yizhizhu222/Robot/Software/Upper_Computer/OrangePi-ZERO3.pdf

D | D

# 1.Note that the voltage of SOC GPIO must matches the

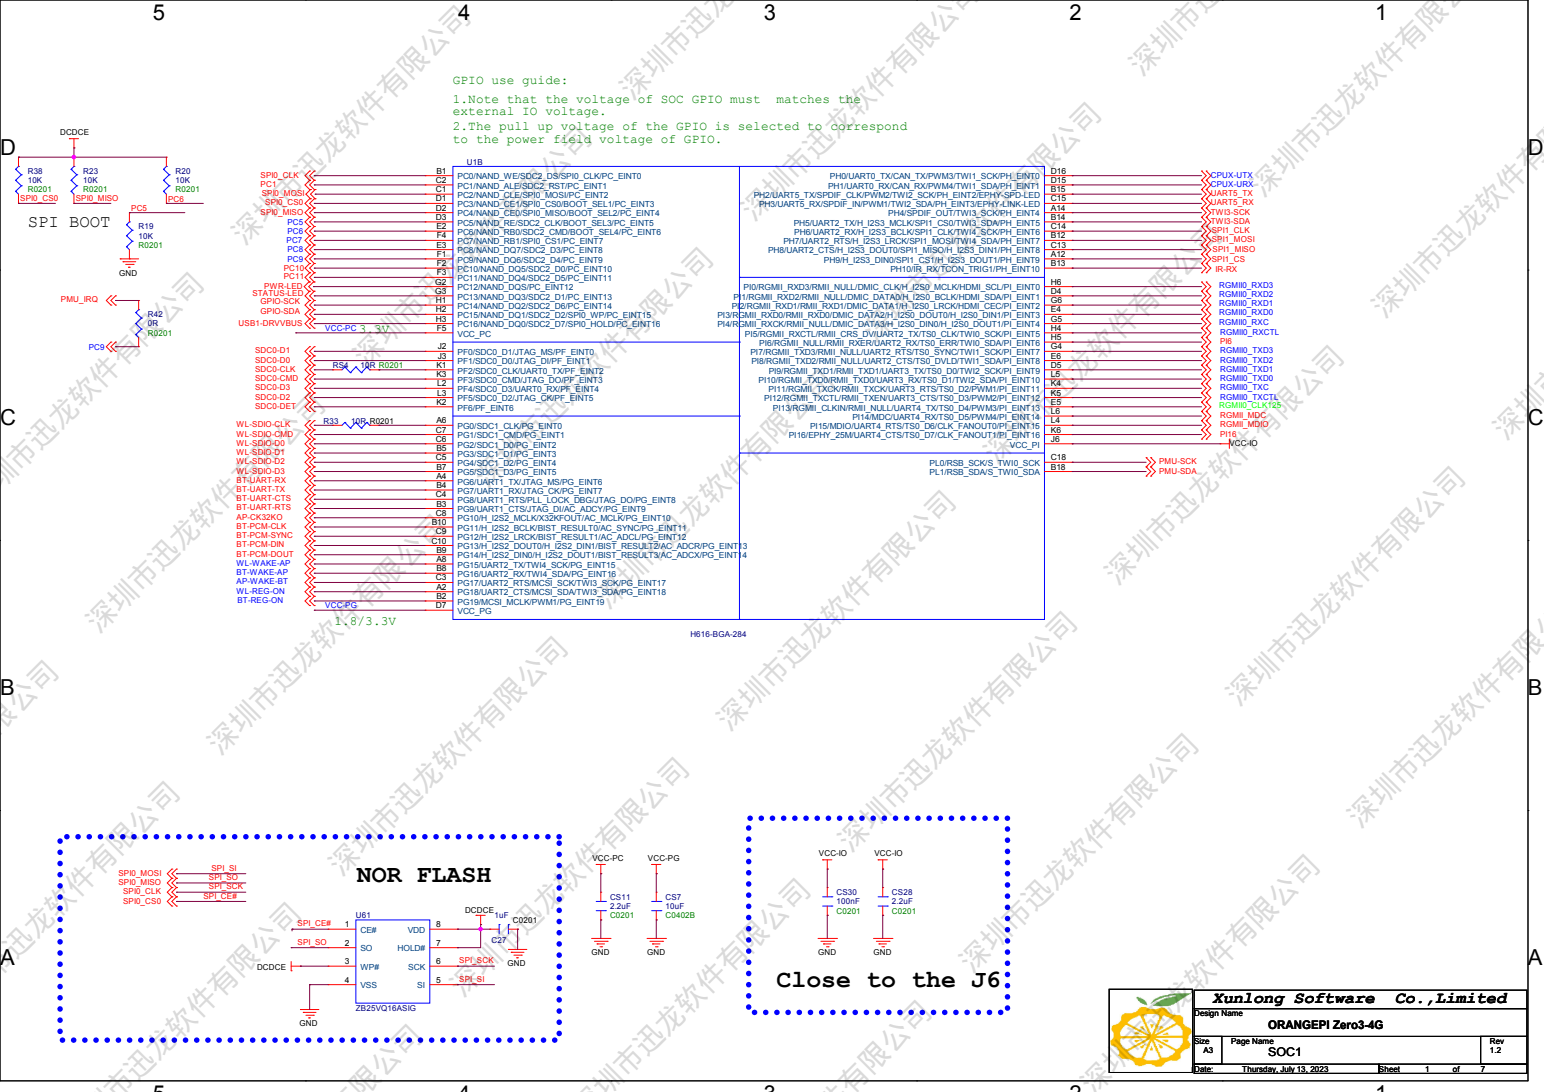
[picture p6: page 1]

深圳市迅龙软件有限公司 深圳市迅龙软件有限公司 深圳市迅龙软件有限公司 深圳市迅龙软件有限公司 深圳市迅龙软件有限公司 深圳市迅龙软件有限公司 深圳市迅龙软件有限公司 深圳市迅龙软件有限公司 深圳市迅龙软件有限公司 深圳市迅龙软件有限公司 深圳市迅龙软件有限公司 深圳市迅龙软件有限公司 深圳市迅龙软件有限公司 深圳市迅龙软件有限公司 深圳市迅龙软件有限公司 深圳市迅龙软件有限公司 深圳市迅龙软件有限公司 深圳市迅龙软件有限公司 深圳市迅龙软件有限公司 深圳市迅龙软件有限公司 深圳市迅龙软件有限公司 深圳市迅龙软件有限公司 深圳市迅龙软件有限公司 深圳市迅龙软件有限公司 深圳市迅龙软件有限公司 深圳市迅龙软件有限公司 深圳市迅龙软件有限公司 深圳市迅龙软件有限公司 深圳市迅龙软件有限公司 深圳市迅龙软件有限公司 深圳市迅龙软件有限公司 深圳市迅龙软件有限公司 深圳市迅龙软件有限公司 深圳市迅龙软件有限公司 深圳市迅龙软件有限公司 深圳市迅龙软件有限公司 深圳市迅龙软件有限公司 深圳市迅龙软件有限公司 深圳市迅龙软件有限公司 深圳市迅龙软件有限公司

GPIO use guide:
external IO voltage.
2.The pull up voltage of the GPIO is selected to correspond
to the power field voltage of GPIO.

Xunlong Software Co.,Limited

D | D

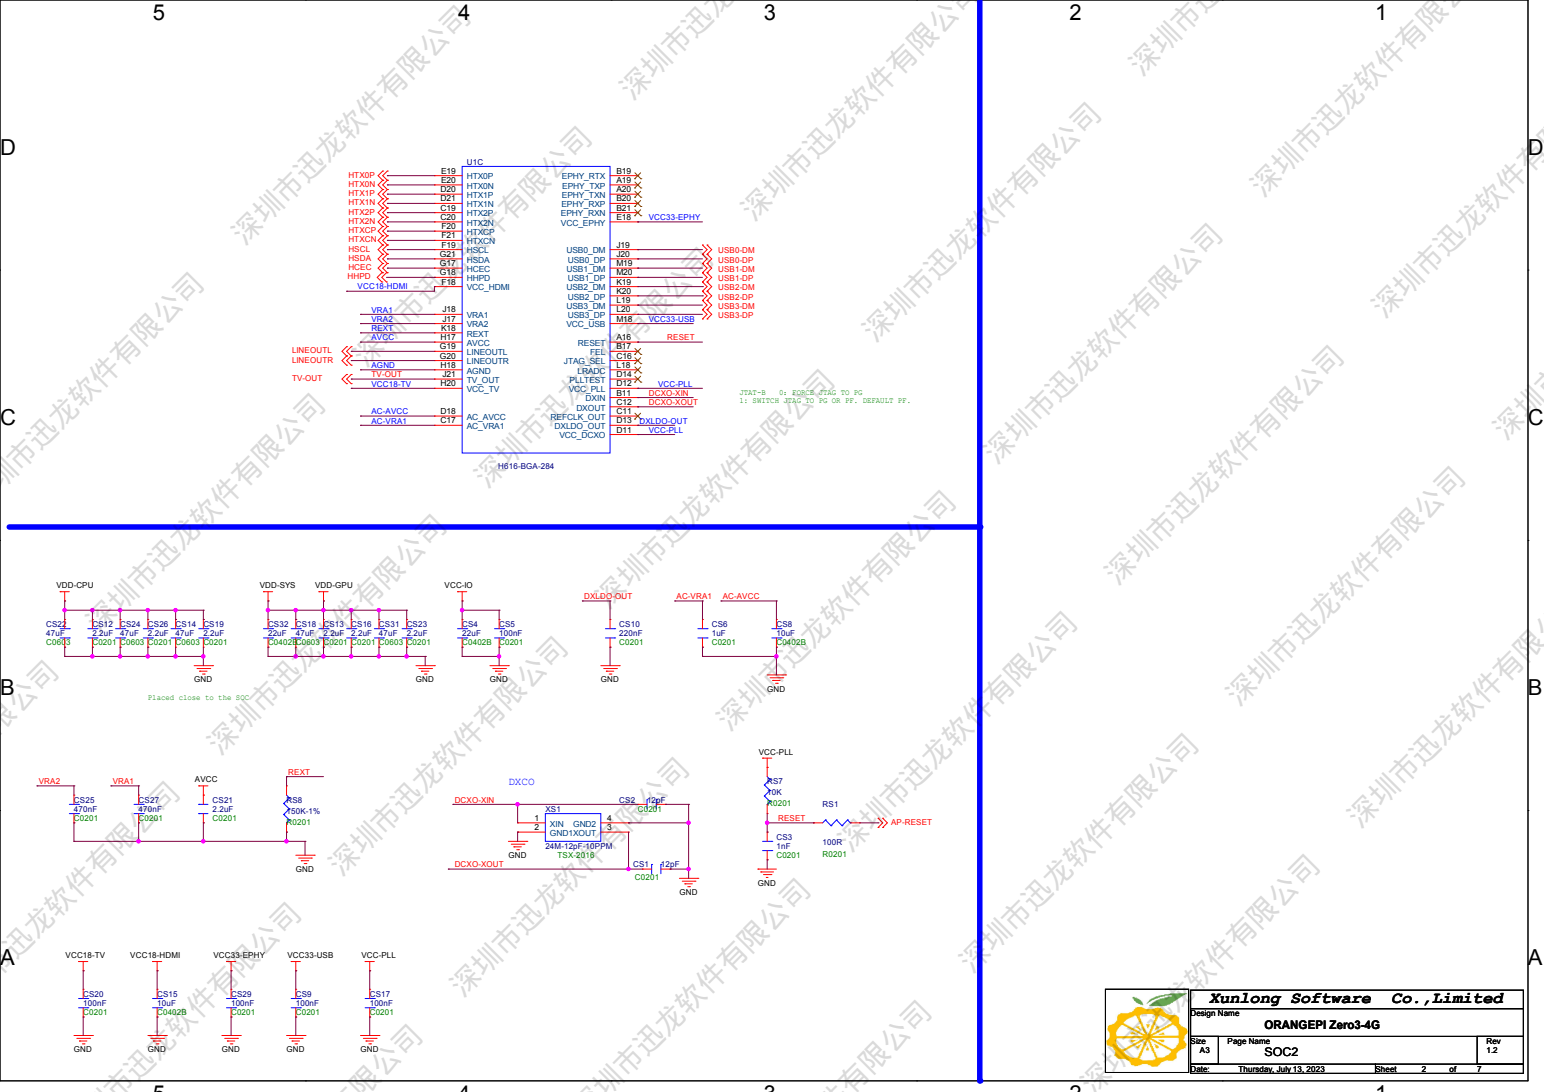
[picture p7: page 2]

深圳市迅龙软件有限公司 深圳市迅龙软件有限公司 深圳市迅龙软件有限公司 深圳市迅龙软件有限公司 深圳市迅龙软件有限公司 深圳市迅龙软件有限公司 深圳市迅龙软件有限公司 深圳市迅龙软件有限公司 深圳市迅龙软件有限公司 深圳市迅龙软件有限公司 深圳市迅龙软件有限公司 深圳市迅龙软件有限公司 深圳市迅龙软件有限公司 深圳市迅龙软件有限公司 深圳市迅龙软件有限公司 深圳市迅龙软件有限公司 深圳市迅龙软件有限公司 深圳市迅龙软件有限公司 深圳市迅龙软件有限公司 深圳市迅龙软件有限公司 深圳市迅龙软件有限公司 深圳市迅龙软件有限公司 深圳市迅龙软件有限公司 深圳市迅龙软件有限公司 深圳市迅龙软件有限公司 深圳市迅龙软件有限公司 深圳市迅龙软件有限公司 深圳市迅龙软件有限公司 深圳市迅龙软件有限公司 深圳市迅龙软件有限公司 深圳市迅龙软件有限公司 深圳市迅龙软件有限公司 深圳市迅龙软件有限公司 深圳市迅龙软件有限公司 深圳市迅龙软件有限公司 深圳市迅龙软件有限公司 深圳市迅龙软件有限公司 深圳市迅龙软件有限公司 深圳市迅龙软件有限公司 深圳市迅龙软件有限公司

JTAT-B 0：FORCE JTAG TO PG
1: SWITCH JTAG TO PG OR PF. DEFAULT PF.

Placed close to the SOC

Xunlong Software Co.,Limited

D | D

# LPDDR4

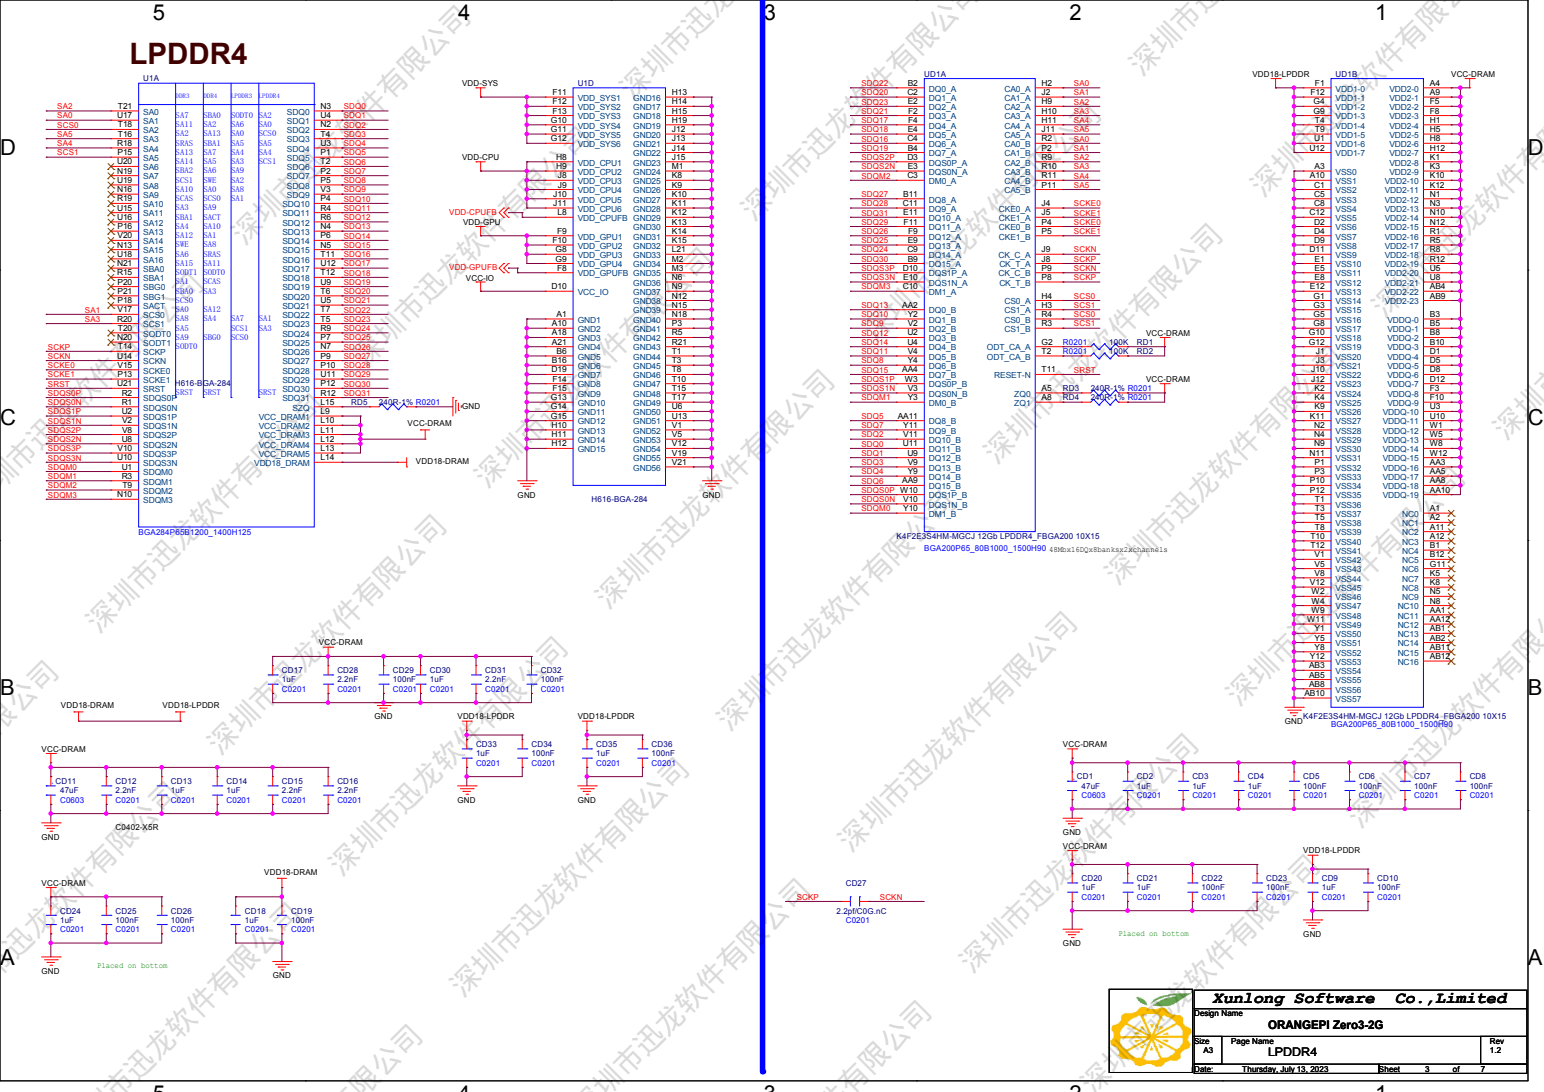
[picture p8: page 3]

深圳市迅龙软件有限公司 深圳市迅龙软件有限公司 深圳市迅龙软件有限公司 深圳市迅龙软件有限公司 深圳市迅龙软件有限公司 深圳市迅龙软件有限公司 深圳市迅龙软件有限公司 深圳市迅龙软件有限公司 深圳市迅龙软件有限公司 深圳市迅龙软件有限公司 深圳市迅龙软件有限公司 深圳市迅龙软件有限公司 深圳市迅龙软件有限公司 深圳市迅龙软件有限公司 深圳市迅龙软件有限公司 深圳市迅龙软件有限公司 深圳市迅龙软件有限公司 深圳市迅龙软件有限公司 深圳市迅龙软件有限公司 深圳市迅龙软件有限公司 深圳市迅龙软件有限公司 深圳市迅龙软件有限公司 深圳市迅龙软件有限公司 深圳市迅龙软件有限公司 深圳市迅龙软件有限公司 深圳市迅龙软件有限公司 深圳市迅龙软件有限公司 深圳市迅龙软件有限公司 深圳市迅龙软件有限公司 深圳市迅龙软件有限公司 深圳市迅龙软件有限公司 深圳市迅龙软件有限公司 深圳市迅龙软件有限公司 深圳市迅龙软件有限公司 深圳市迅龙软件有限公司 深圳市迅龙软件有限公司 深圳市迅龙软件有限公司 深圳市迅龙软件有限公司 深圳市迅龙软件有限公司 深圳市迅龙软件有限公司

Xunlong Software Co.,Limited

# TPYE-C

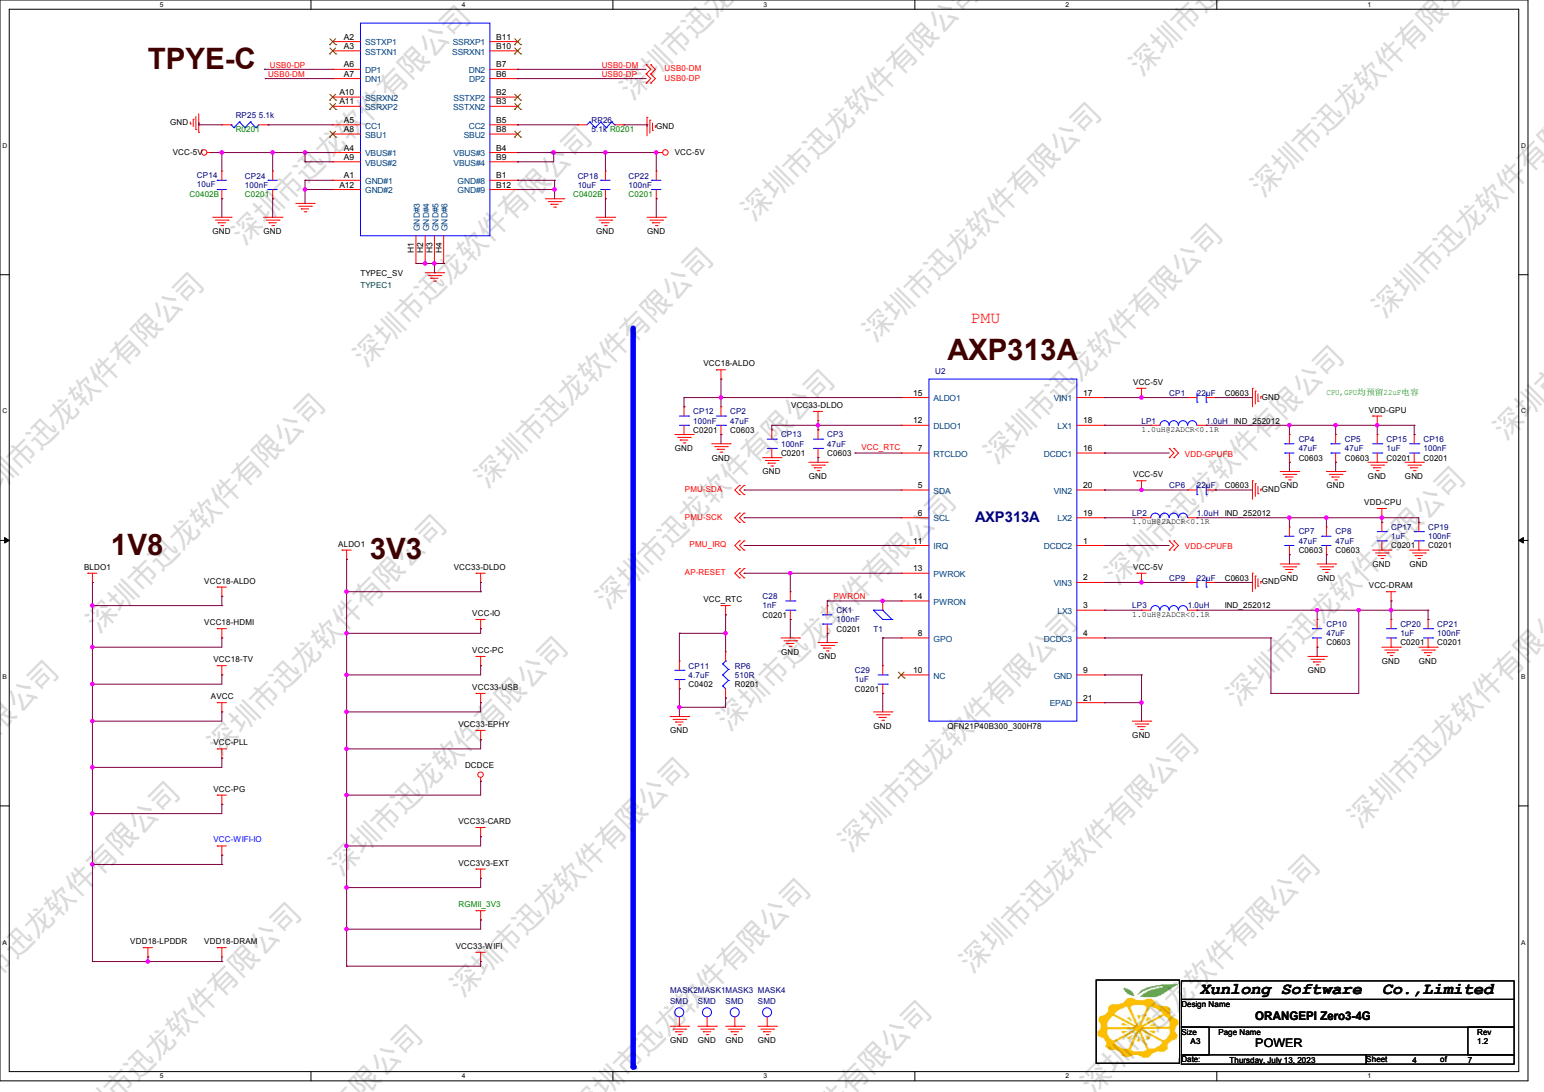
[picture p9: page 4]

深圳市迅龙软件有限公司 深圳市迅龙软件有限公司 深圳市迅龙软件有限公司 深圳市迅龙软件有限公司 深圳市迅龙软件有限公司 深圳市迅龙软件有限公司 深圳市迅龙软件有限公司 深圳市迅龙软件有限公司 深圳市迅龙软件有限公司 深圳市迅龙软件有限公司 深圳市迅龙软件有限公司 深圳市迅龙软件有限公司 深圳市迅龙软件有限公司 深圳市迅龙软件有限公司 深圳市迅龙软件有限公司 深圳市迅龙软件有限公司 深圳市迅龙软件有限公司 深圳市迅龙软件有限公司 深圳市迅龙软件有限公司 深圳市迅龙软件有限公司 深圳市迅龙软件有限公司 深圳市迅龙软件有限公司 深圳市迅龙软件有限公司 深圳市迅龙软件有限公司 深圳市迅龙软件有限公司 深圳市迅龙软件有限公司 深圳市迅龙软件有限公司 深圳市迅龙软件有限公司 深圳市迅龙软件有限公司 深圳市迅龙软件有限公司 深圳市迅龙软件有限公司 深圳市迅龙软件有限公司 深圳市迅龙软件有限公司 深圳市迅龙软件有限公司 深圳市迅龙软件有限公司 深圳市迅龙软件有限公司 深圳市迅龙软件有限公司 深圳市迅龙软件有限公司 深圳市迅龙软件有限公司 深圳市迅龙软件有限公司

Xunlong Software Co.,Limited

D | D

# T CARD

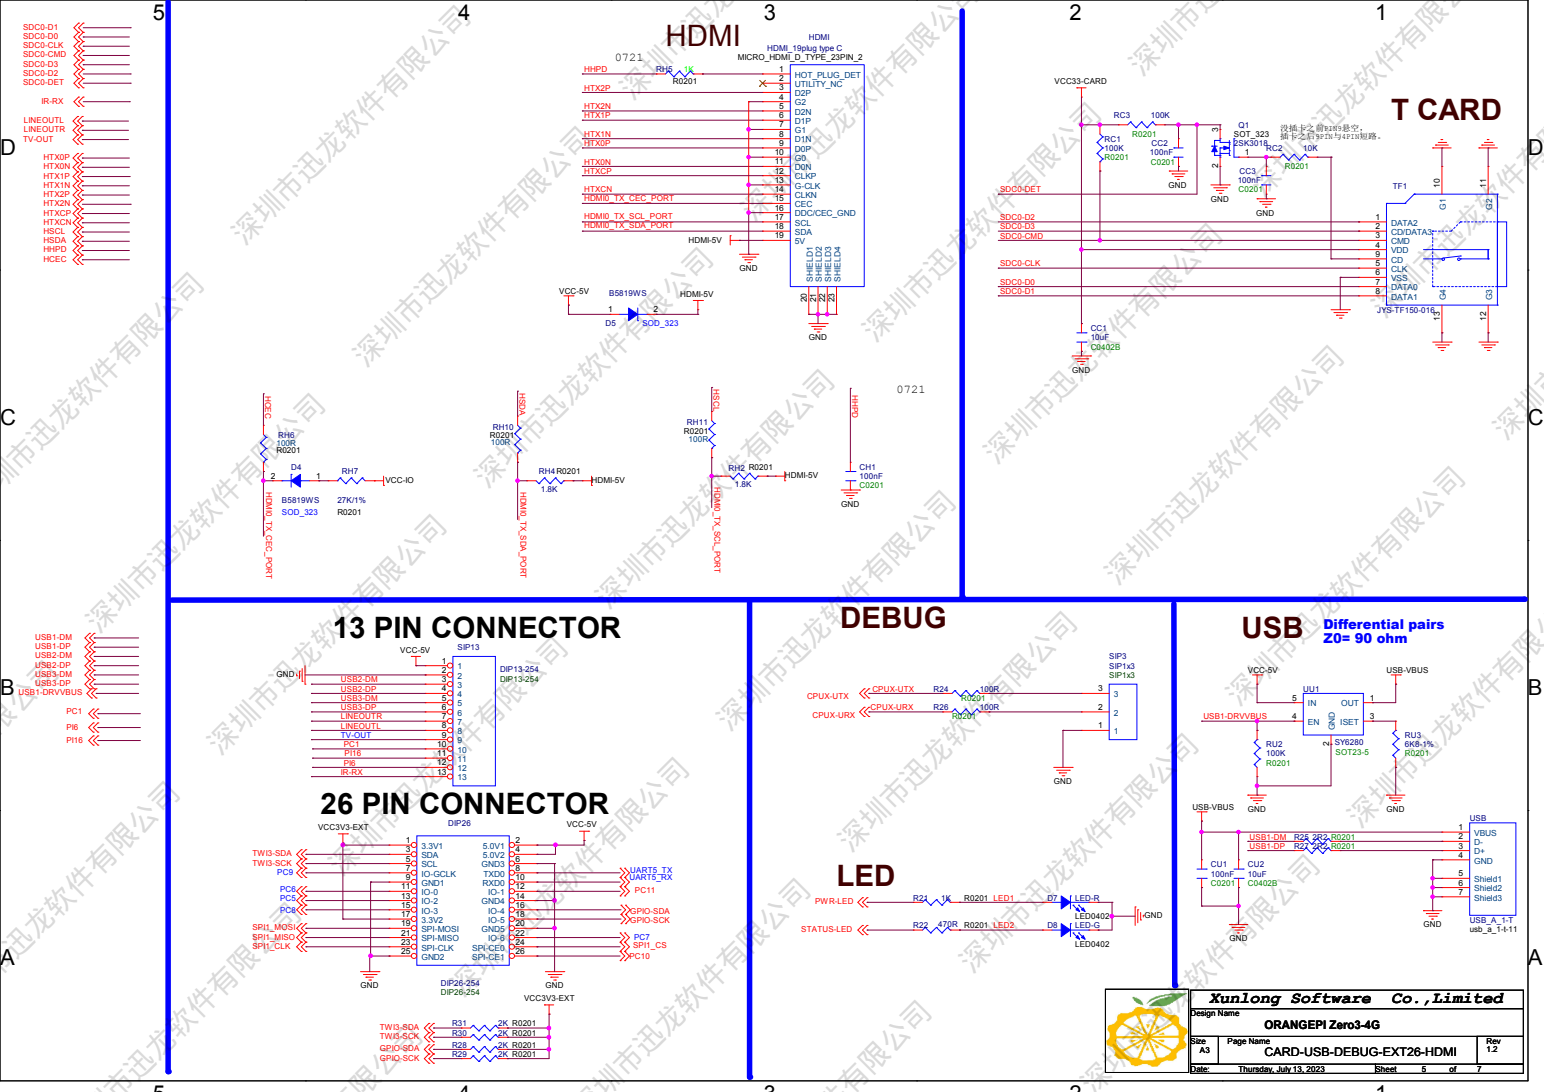
[picture p10: page 5]

深圳市迅龙软件有限公司 深圳市迅龙软件有限公司 深圳市迅龙软件有限公司 深圳市迅龙软件有限公司 深圳市迅龙软件有限公司 深圳市迅龙软件有限公司 深圳市迅龙软件有限公司 深圳市迅龙软件有限公司 深圳市迅龙软件有限公司 深圳市迅龙软件有限公司 深圳市迅龙软件有限公司 深圳市迅龙软件有限公司 深圳市迅龙软件有限公司 深圳市迅龙软件有限公司 深圳市迅龙软件有限公司 深圳市迅龙软件有限公司 深圳市迅龙软件有限公司 深圳市迅龙软件有限公司 深圳市迅龙软件有限公司 深圳市迅龙软件有限公司 深圳市迅龙软件有限公司 深圳市迅龙软件有限公司 深圳市迅龙软件有限公司 深圳市迅龙软件有限公司 深圳市迅龙软件有限公司 深圳市迅龙软件有限公司 深圳市迅龙软件有限公司 深圳市迅龙软件有限公司 深圳市迅龙软件有限公司 深圳市迅龙软件有限公司 深圳市迅龙软件有限公司 深圳市迅龙软件有限公司 深圳市迅龙软件有限公司 深圳市迅龙软件有限公司 深圳市迅龙软件有限公司 深圳市迅龙软件有限公司 深圳市迅龙软件有限公司 深圳市迅龙软件有限公司 深圳市迅龙软件有限公司 深圳市迅龙软件有限公司

Xunlong Software Co.,Limited

CARD-USB-DEBUG-EXT26-HDMI

# Differential pairs Z0= 100 ohm

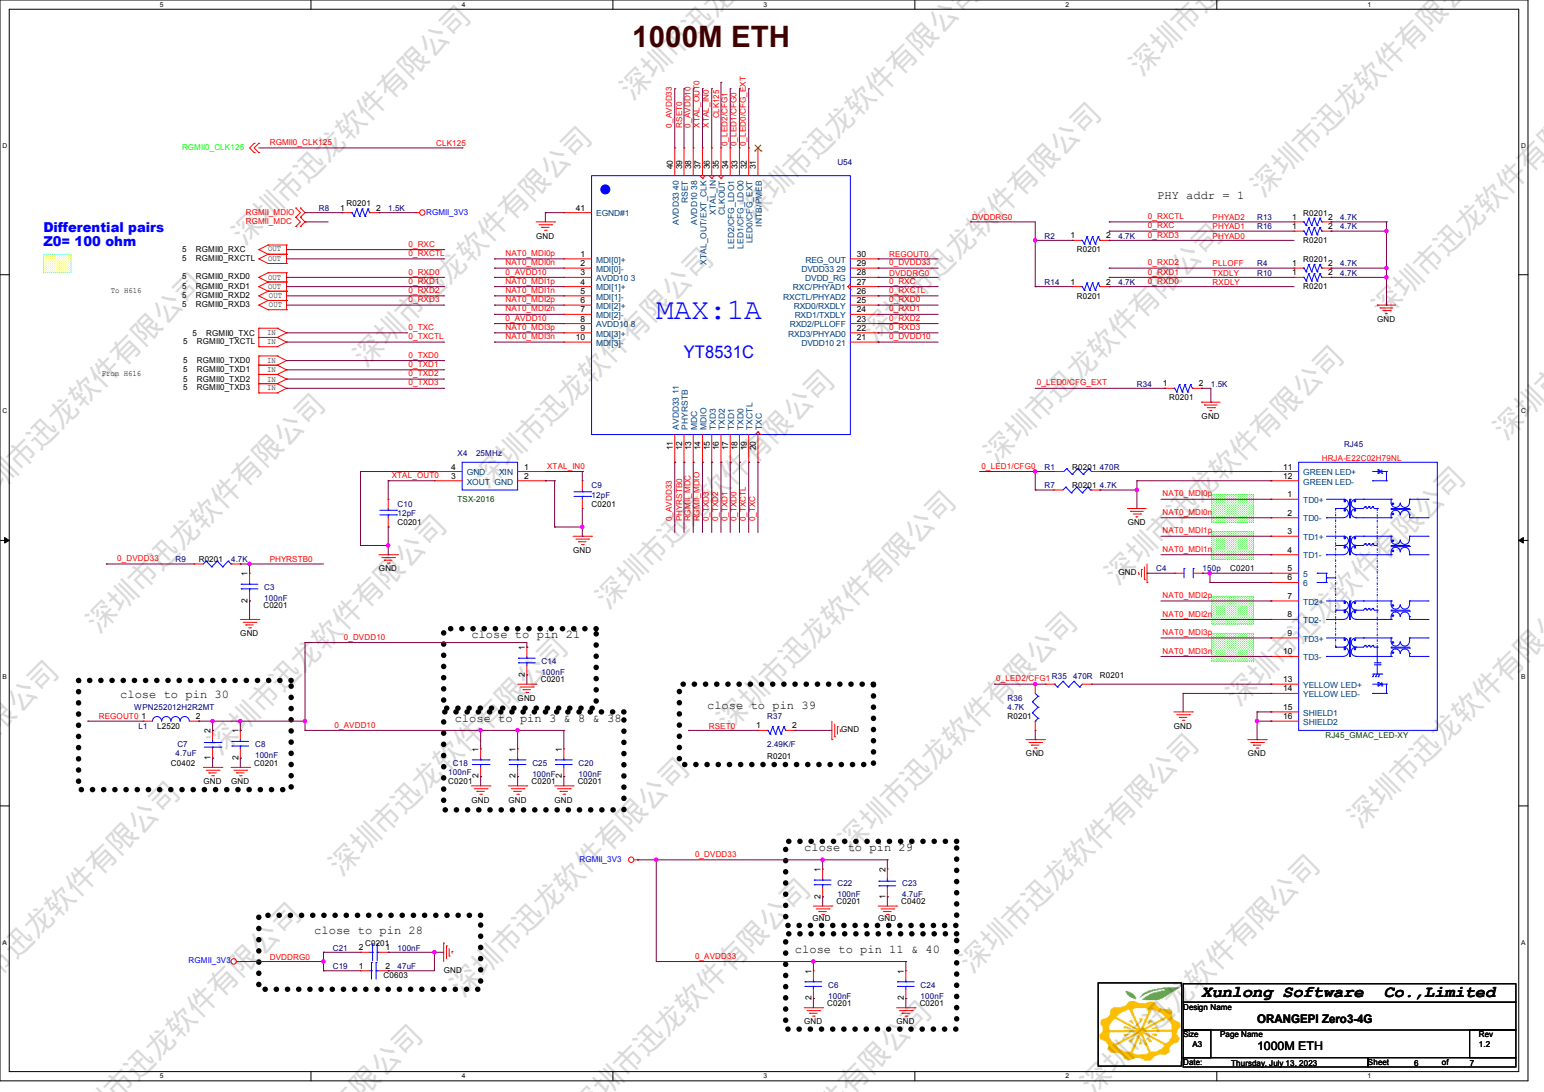
[picture p11: page 6]

深圳市迅龙软件有限公司 深圳市迅龙软件有限公司 深圳市迅龙软件有限公司 深圳市迅龙软件有限公司 深圳市迅龙软件有限公司 深圳市迅龙软件有限公司 深圳市迅龙软件有限公司 深圳市迅龙软件有限公司 深圳市迅龙软件有限公司 深圳市迅龙软件有限公司 深圳市迅龙软件有限公司 深圳市迅龙软件有限公司 深圳市迅龙软件有限公司 深圳市迅龙软件有限公司 深圳市迅龙软件有限公司 深圳市迅龙软件有限公司 深圳市迅龙软件有限公司 深圳市迅龙软件有限公司 深圳市迅龙软件有限公司 深圳市迅龙软件有限公司 深圳市迅龙软件有限公司 深圳市迅龙软件有限公司 深圳市迅龙软件有限公司 深圳市迅龙软件有限公司 深圳市迅龙软件有限公司 深圳市迅龙软件有限公司 深圳市迅龙软件有限公司 深圳市迅龙软件有限公司 深圳市迅龙软件有限公司 深圳市迅龙软件有限公司 深圳市迅龙软件有限公司 深圳市迅龙软件有限公司 深圳市迅龙软件有限公司 深圳市迅龙软件有限公司 深圳市迅龙软件有限公司 深圳市迅龙软件有限公司 深圳市迅龙软件有限公司 深圳市迅龙软件有限公司 深圳市迅龙软件有限公司 深圳市迅龙软件有限公司

Xunlong Software Co.,Limited

D | D

### 50Ω,TOP参考LAYER3

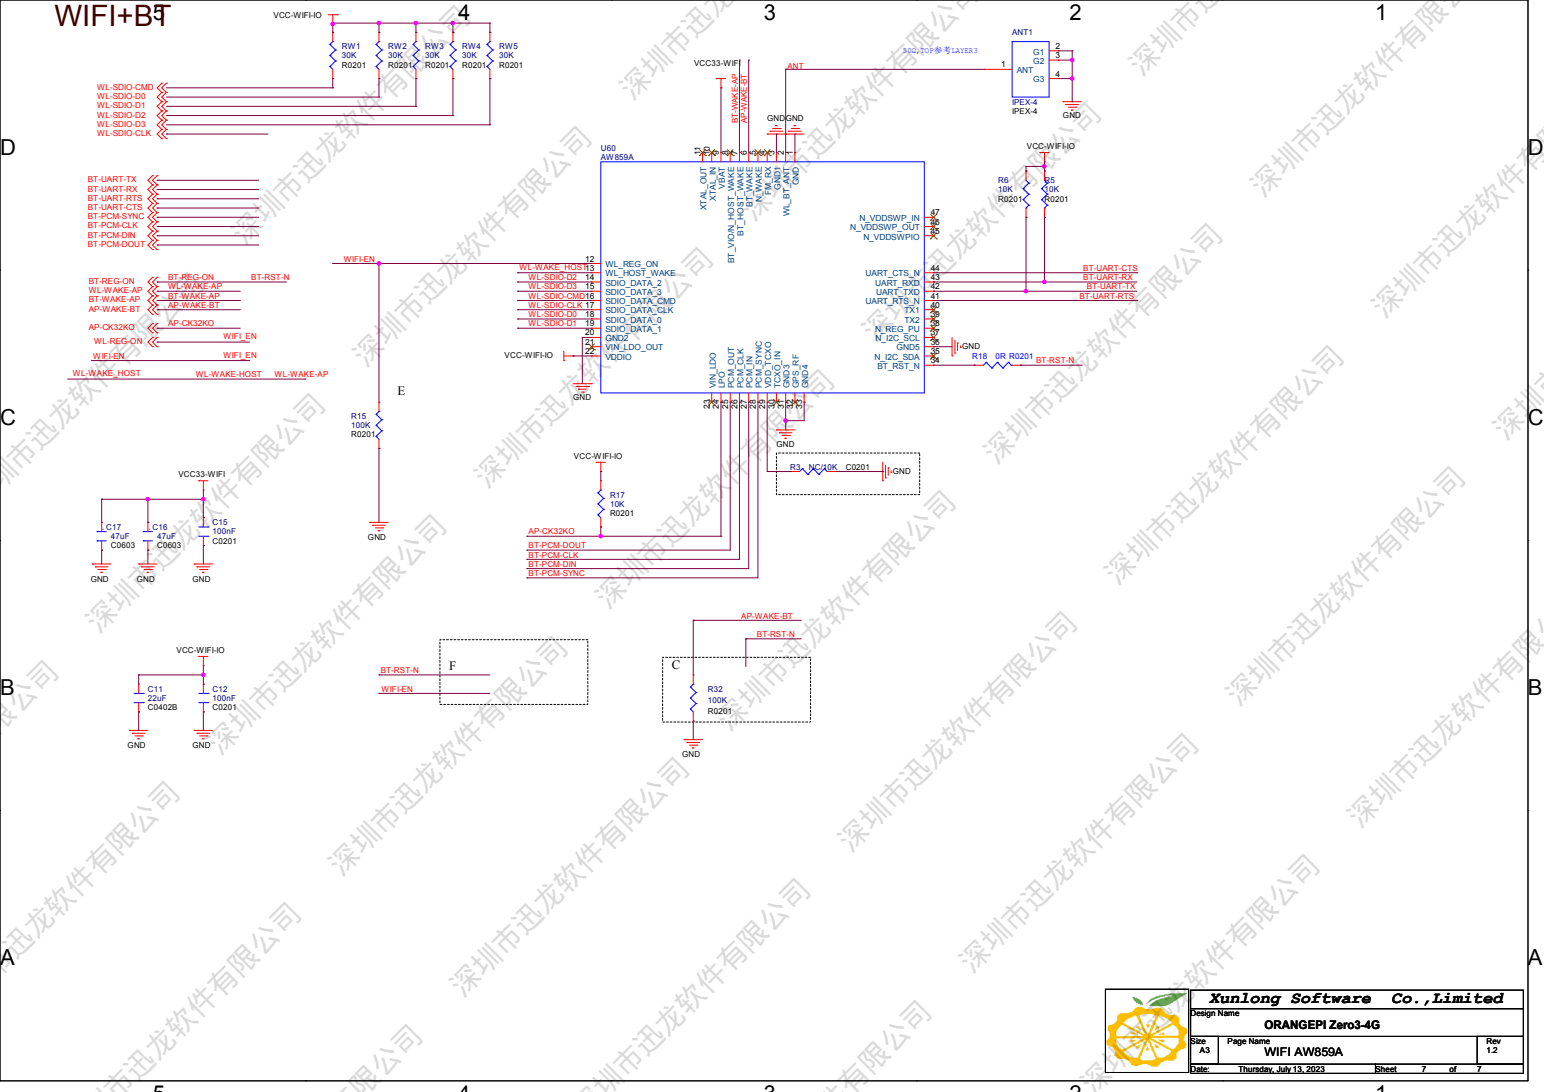
[picture p12: page 7]

深圳市迅龙软件有限公司 深圳市迅龙软件有限公司 深圳市迅龙软件有限公司 深圳市迅龙软件有限公司 深圳市迅龙软件有限公司 深圳市迅龙软件有限公司 深圳市迅龙软件有限公司 深圳市迅龙软件有限公司 深圳市迅龙软件有限公司 深圳市迅龙软件有限公司 深圳市迅龙软件有限公司 深圳市迅龙软件有限公司 深圳市迅龙软件有限公司 深圳市迅龙软件有限公司 深圳市迅龙软件有限公司 深圳市迅龙软件有限公司 深圳市迅龙软件有限公司 深圳市迅龙软件有限公司 深圳市迅龙软件有限公司 深圳市迅龙软件有限公司 深圳市迅龙软件有限公司 深圳市迅龙软件有限公司 深圳市迅龙软件有限公司 深圳市迅龙软件有限公司 深圳市迅龙软件有限公司 深圳市迅龙软件有限公司 深圳市迅龙软件有限公司 深圳市迅龙软件有限公司 深圳市迅龙软件有限公司 深圳市迅龙软件有限公司 深圳市迅龙软件有限公司 深圳市迅龙软件有限公司 深圳市迅龙软件有限公司 深圳市迅龙软件有限公司 深圳市迅龙软件有限公司 深圳市迅龙软件有限公司 深圳市迅龙软件有限公司 深圳市迅龙软件有限公司 深圳市迅龙软件有限公司 深圳市迅龙软件有限公司

Xunlong Software Co.,Limited
